mohamedyanis/BaroAxel-Brain/Images/Block Diagram/BaroAxel_Brain.png

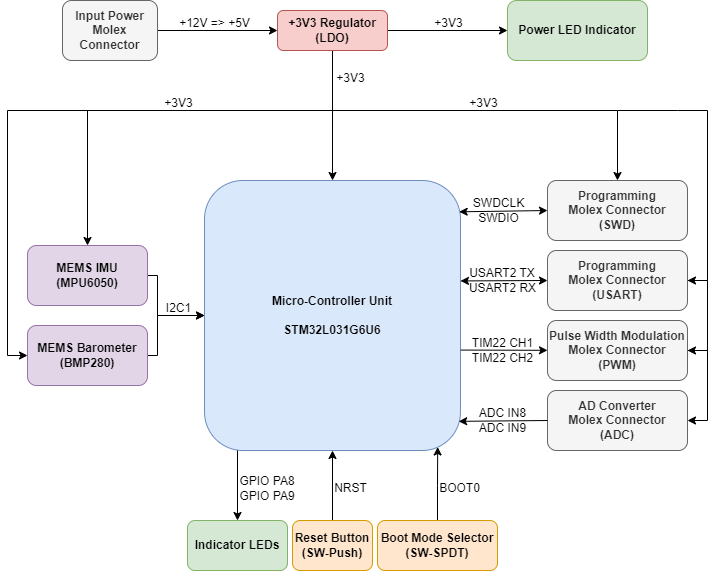
Images/Block Diagram/BaroAxel_Brain.png
