mohamedyanis/BaroAxel-Brain/Images/Block Diagram/BaroAxel_Brain_White_BG.png

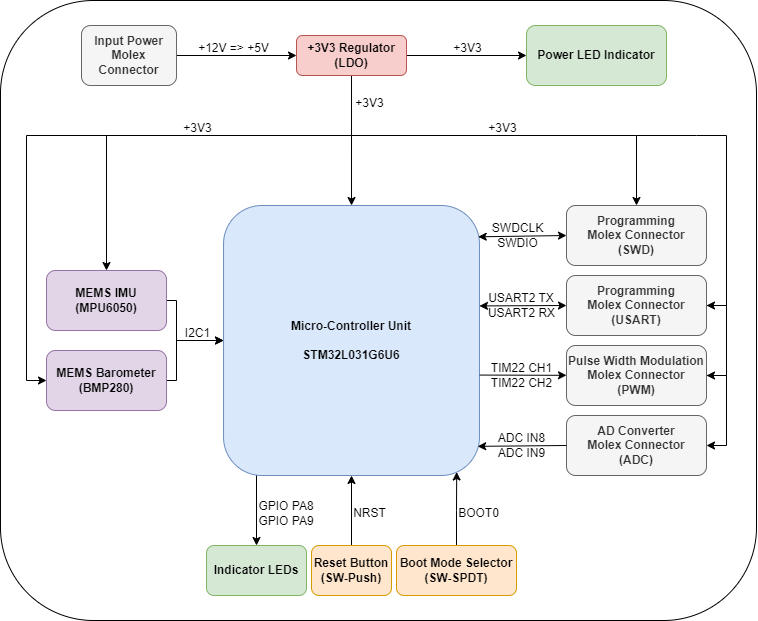
Images/Block Diagram/BaroAxel_Brain_White_BG.png
