mohamedyanis/BaroAxel-Brain/Images/PCB 3D/BaroAxel_Brain_Front.png

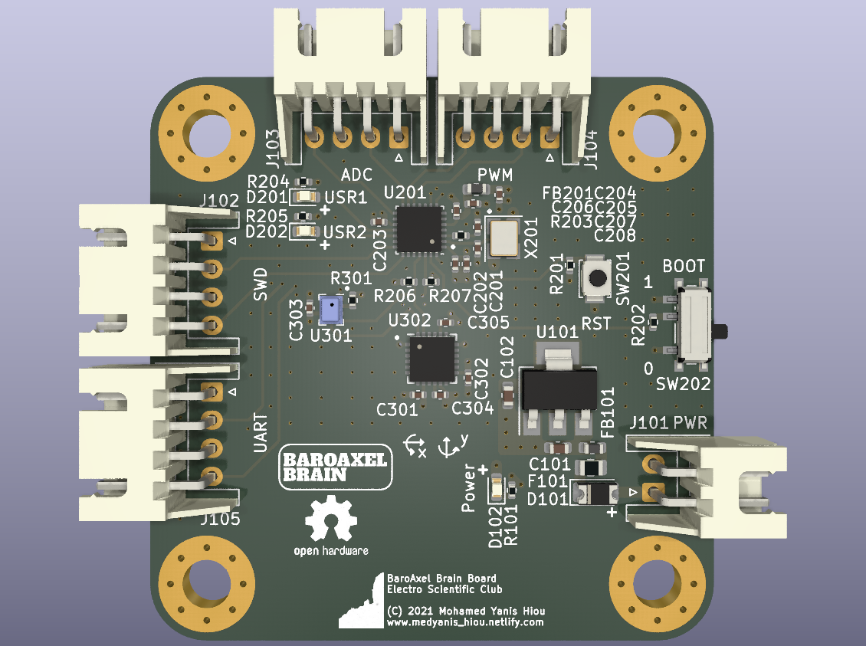
Images/PCB 3D/BaroAxel_Brain_Front.png
