mohamedyanis/BaroAxel-Brain/Images/STM32 Pins Configuration/AxelBar Brain MCU.png

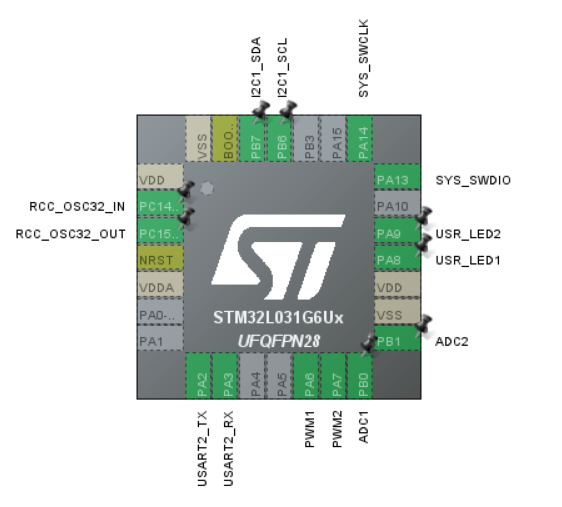
Images/STM32 Pins Configuration/AxelBar Brain MCU.png
