mohamedyanis/BaroAxel-Brain/Firmware Test/BaroAxel_LED_Test/Core/Inc/main.h

#define LED1_Pin GPIO_PIN_8
#define LED1_GPIO_Port GPIOA
#define LED2_Pin GPIO_PIN_9
#define LED2_GPIO_Port GPIOA
