mohamedyanis/BaroAxel-Brain/Firmware Test/BaroAxel_LED_Test/Core/Inc/imu.h

#include "stm32l0xx_hal.h"

void MPU6050_init(void); //Initialize the MPU
void MPU6050_Read_Accel (float *Ax, float *Ay, float *Az); //Read MPU Accelerator
void MPU6050_Read_Gyro (float *Gx, float *Gy, float *Gz); //Read MPU Gyroscope
